JonasSouza871/PolySense-Station-/images/data_analysis/01_Comparison_of_Humidity_Sensor_Distributions_September_Vitória_da_Conquista.png

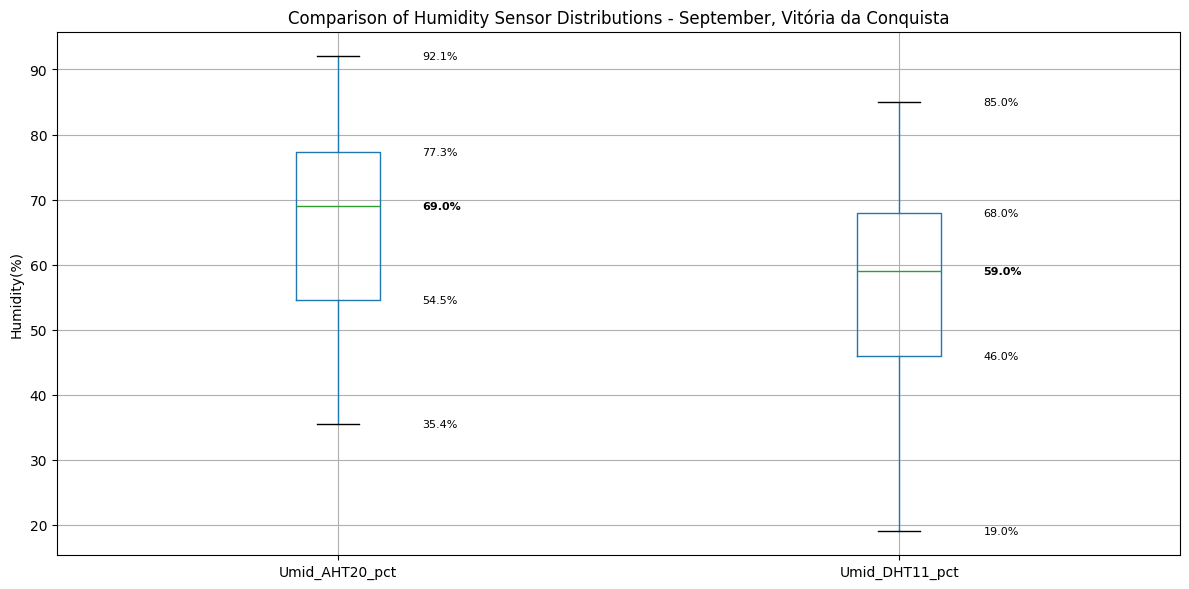
images/data_analysis/01_Comparison_of_Humidity_Sensor_Distributions_September_Vitória_da_Conquista.png
