JonasSouza871/PolySense-Station-/images/data_analysis/01_Humidity_Data_Histogram_in_September_Vitória_da_Conquista.png

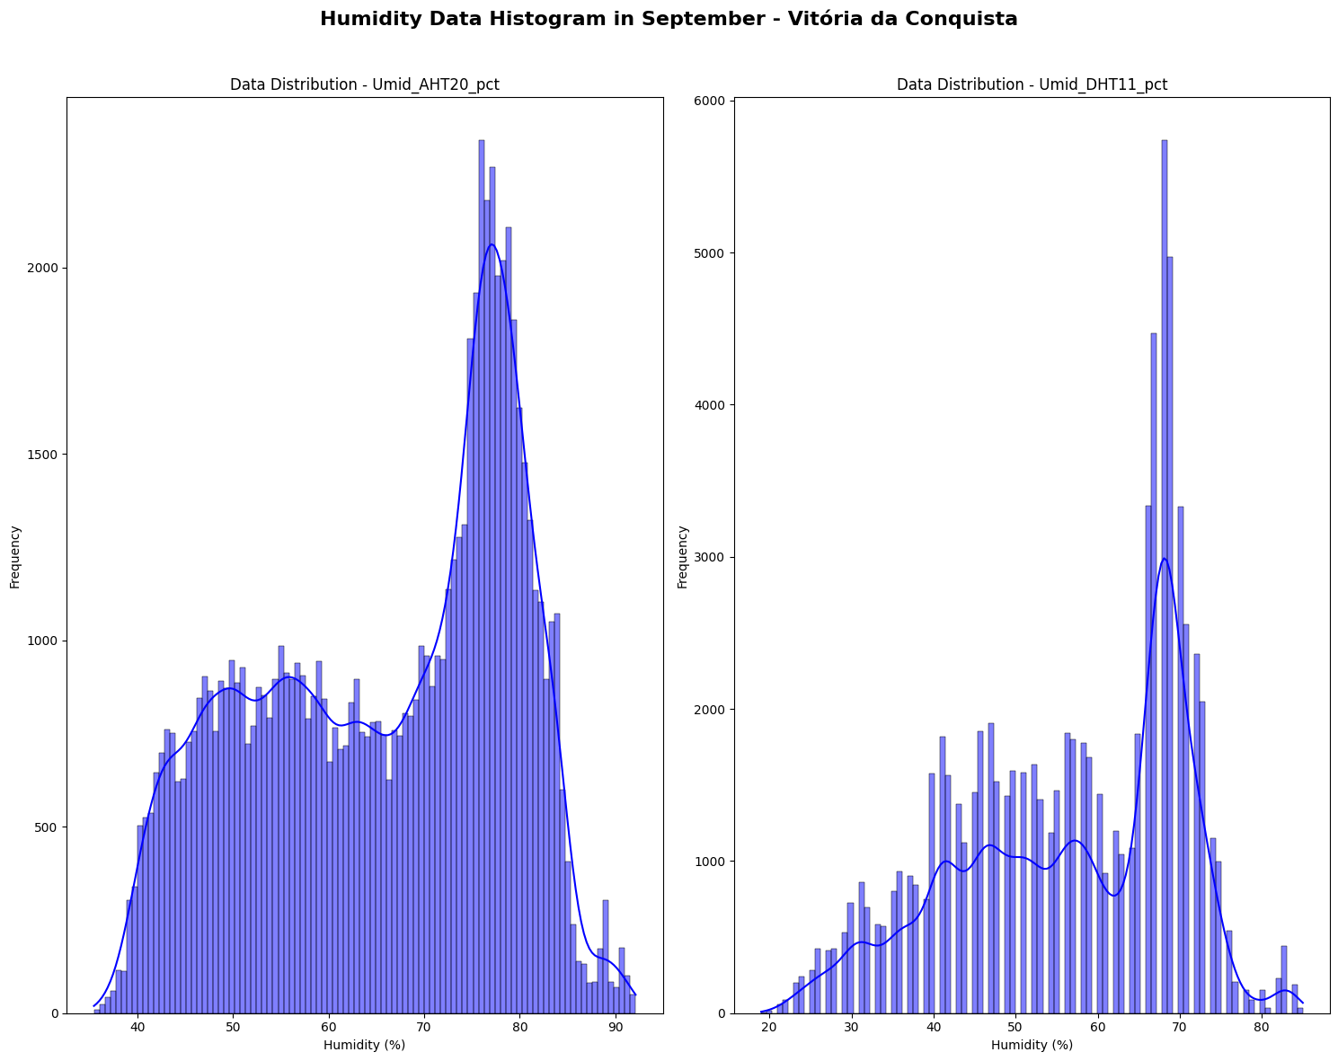
images/data_analysis/01_Humidity_Data_Histogram_in_September_Vitória_da_Conquista.png
