JonasSouza871/PolySense-Station-/images/data_analysis/02_Correlation_Matrix_All_Environmental_SensorsnVitória_da_Conquista_September_2025.png

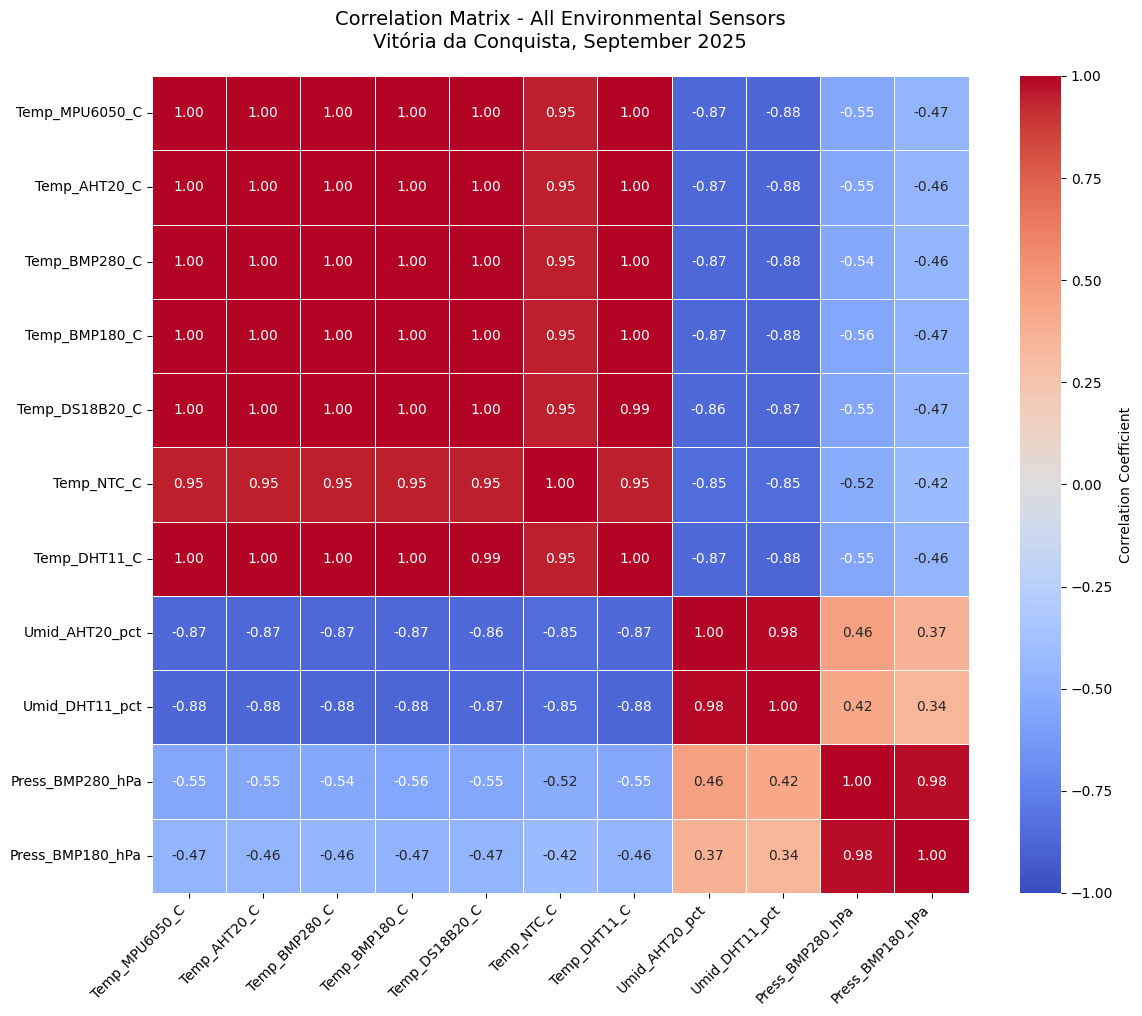
images/data_analysis/02_Correlation_Matrix_All_Environmental_SensorsnVitória_da_Conquista_September_2025.png
