JonasSouza871/PolySense-Station-/images/data_analysis/02_Relationship_between_Humidity_AHT20_and_Pressure_BMP180nVitória_da_Conquista_September_2025.png

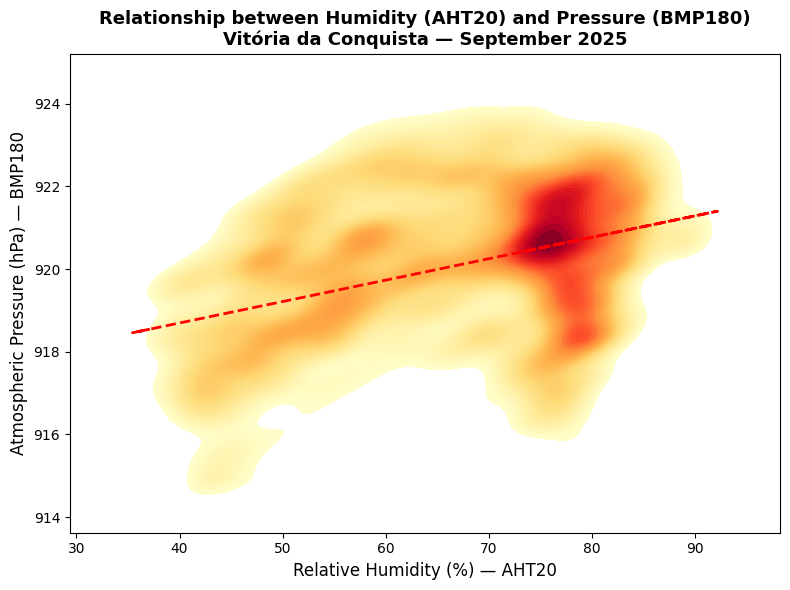
images/data_analysis/02_Relationship_between_Humidity_AHT20_and_Pressure_BMP180nVitória_da_Conquista_September_2025.png
