JonasSouza871/PolySense-Station-/images/data_analysis/02_Relationship_between_Temperature_BMP280_and_Humidity_AHT20nVitória_da_Conquista_September_2025.png

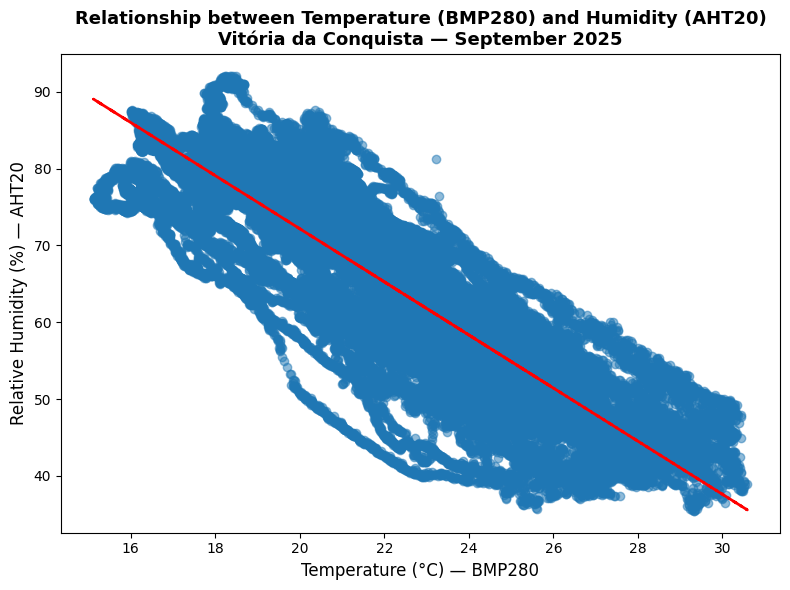
images/data_analysis/02_Relationship_between_Temperature_BMP280_and_Humidity_AHT20nVitória_da_Conquista_September_2025.png
