JonasSouza871/PolySense-Station-/images/data_analysis/03_Data_Completeness_per_Humidity_Sensor_Vitória_da_Conquista_September_2025.png

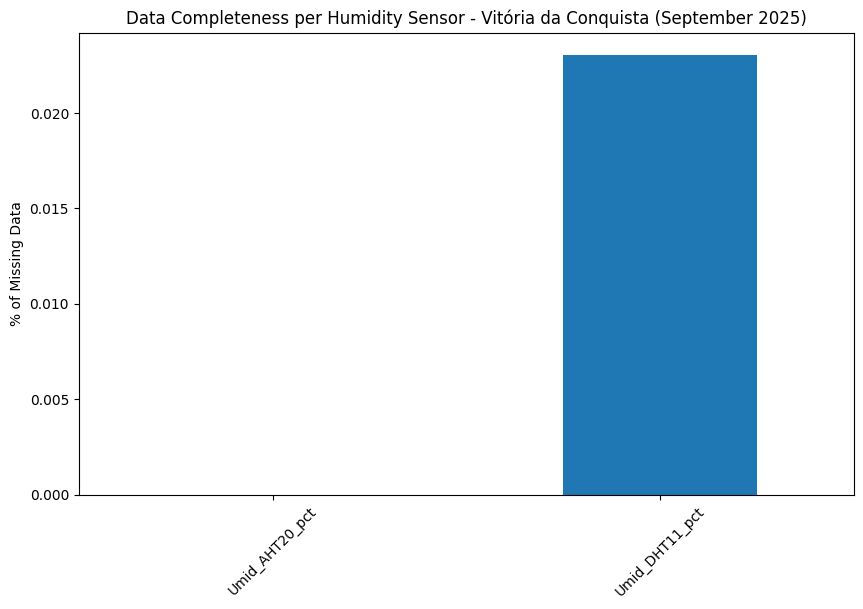
images/data_analysis/03_Data_Completeness_per_Humidity_Sensor_Vitória_da_Conquista_September_2025.png
