JonasSouza871/PolySense-Station-/images/data_analysis/04_BLAND_ALTMAN_ANALYSIS_Humidity_Sensors_vs_Reference_Umi_Ins.png

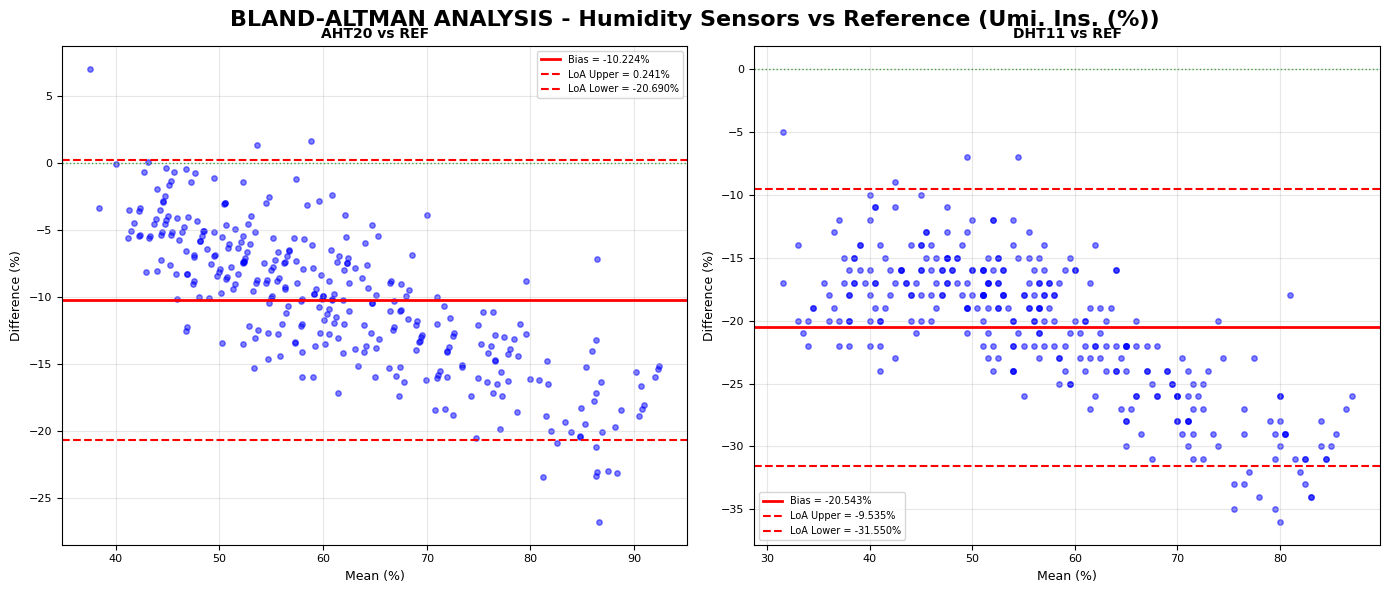
images/data_analysis/04_BLAND_ALTMAN_ANALYSIS_Humidity_Sensors_vs_Reference_Umi_Ins.png
