JonasSouza871/PolySense-Station-/images/data_analysis/04_BLAND_ALTMAN_ANALYSIS_Pressure_Sensors_BMP280_vs_BMP180.png

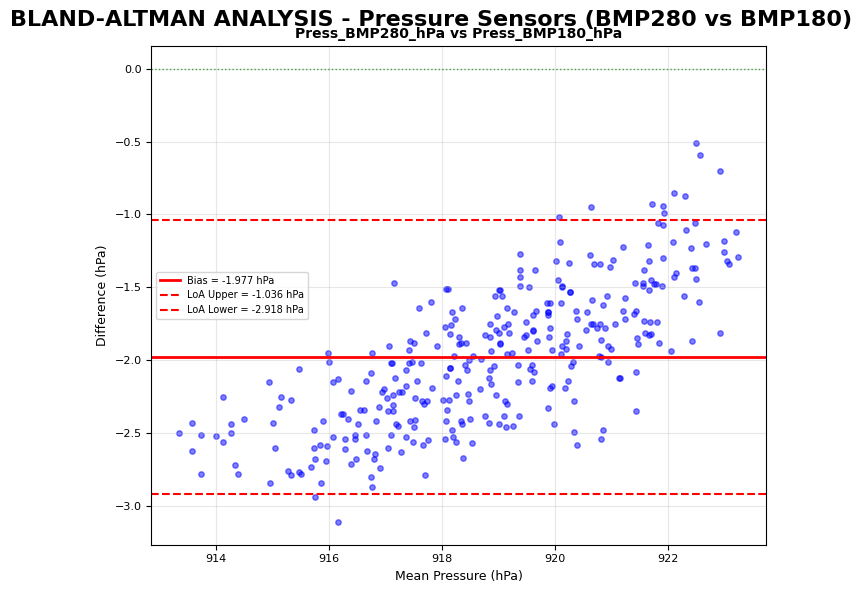
images/data_analysis/04_BLAND_ALTMAN_ANALYSIS_Pressure_Sensors_BMP280_vs_BMP180.png
