JonasSouza871/PolySense-Station-/images/data_analysis/04_BLAND_ALTMAN_ANALYSIS_Pressure_Sensors_vs_Reference_Pressao_Ins_hPa.png

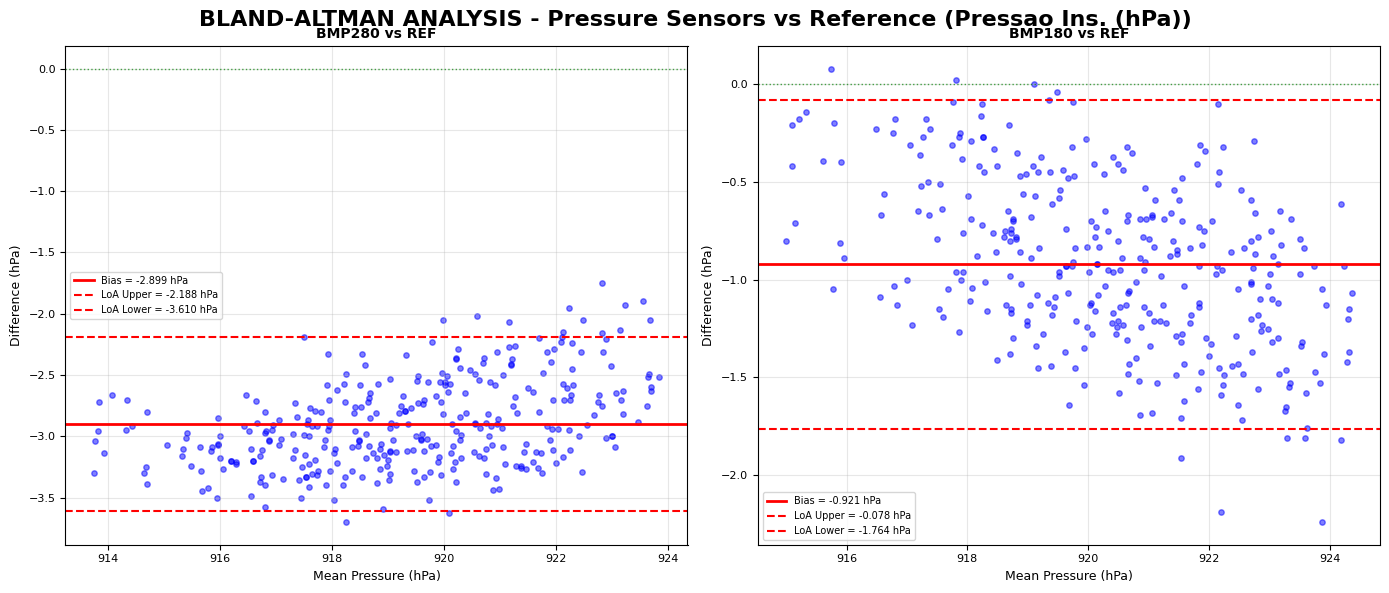
images/data_analysis/04_BLAND_ALTMAN_ANALYSIS_Pressure_Sensors_vs_Reference_Pressao_Ins_hPa.png
