JonasSouza871/PolySense-Station-/images/data_analysis/04_BLAND_ALTMAN_ANALYSIS_Sensors_vs_Reference_Temp_Ins_C.png

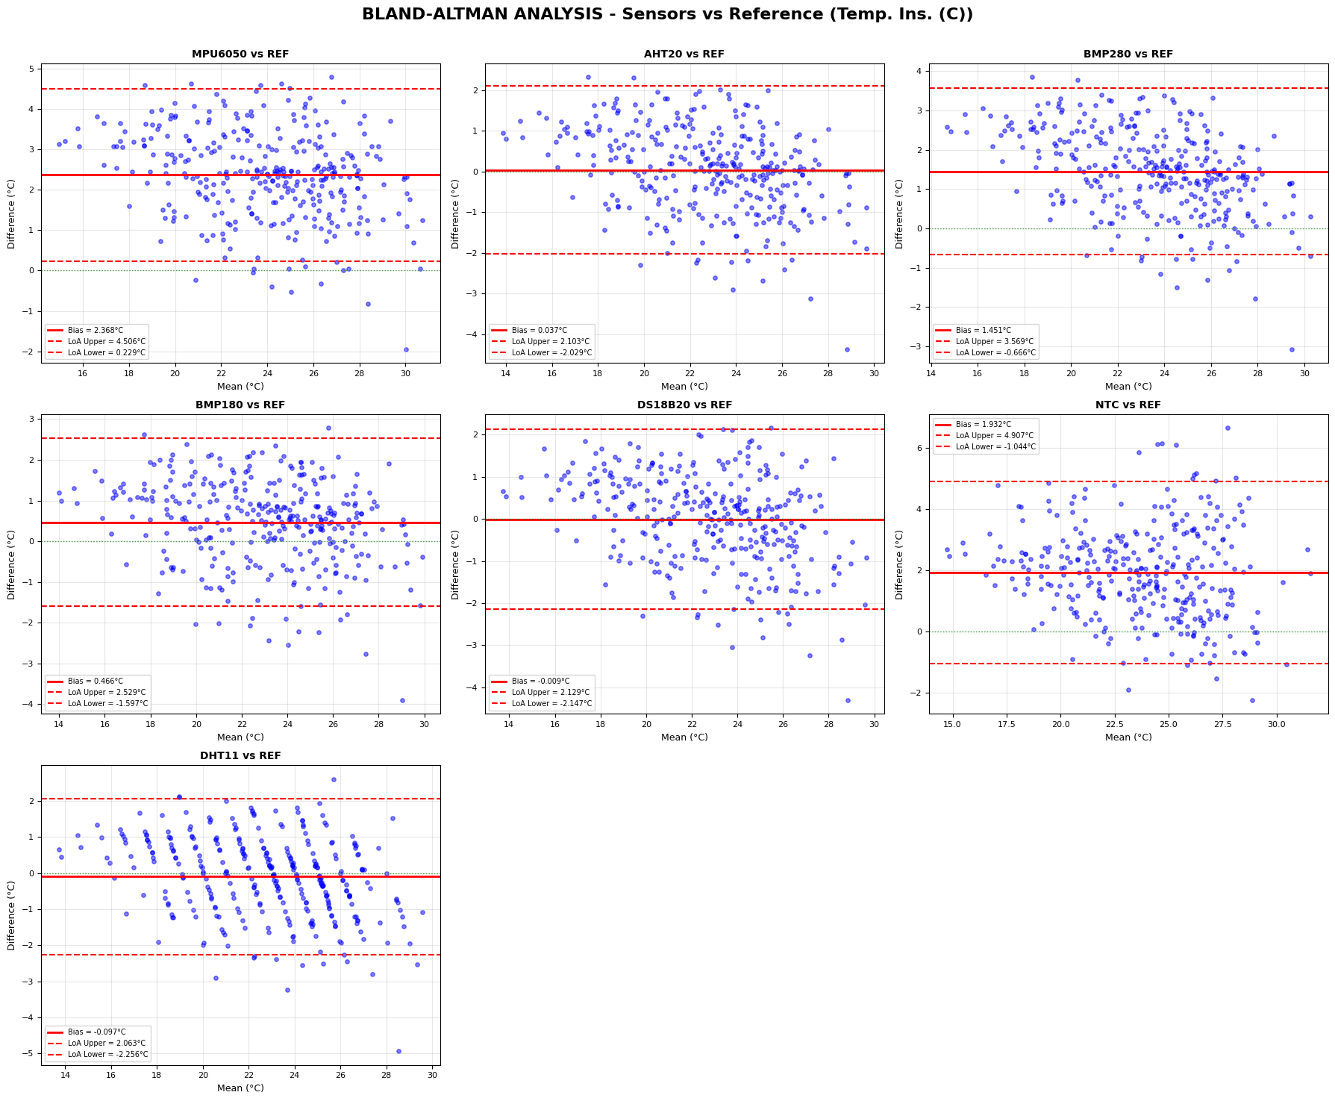
images/data_analysis/04_BLAND_ALTMAN_ANALYSIS_Sensors_vs_Reference_Temp_Ins_C.png
