JonasSouza871/PolySense-Station-/images/data_analysis/04_BLAND_ALTMAN_ANALYSIS_Temperature_Sensors_Pairwise_Comparison.png

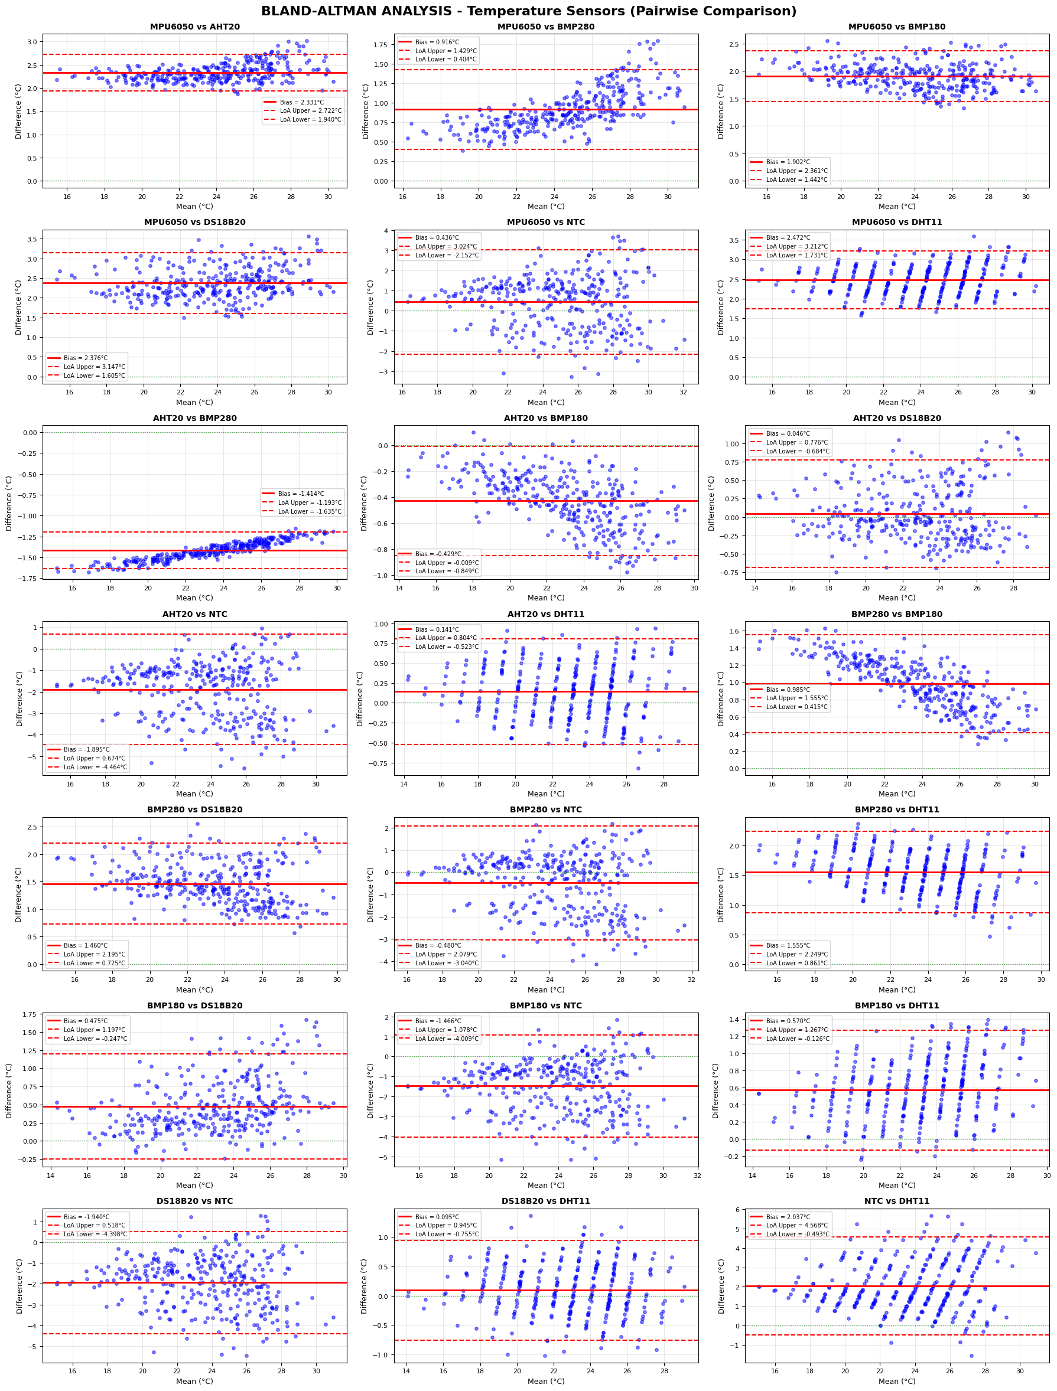
images/data_analysis/04_BLAND_ALTMAN_ANALYSIS_Temperature_Sensors_Pairwise_Comparison.png
