JonasSouza871/PolySense-Station-/images/data_analysis/05_Humidity_Sensors_Comparison_September_2025_Vitória_da_Conquista.png

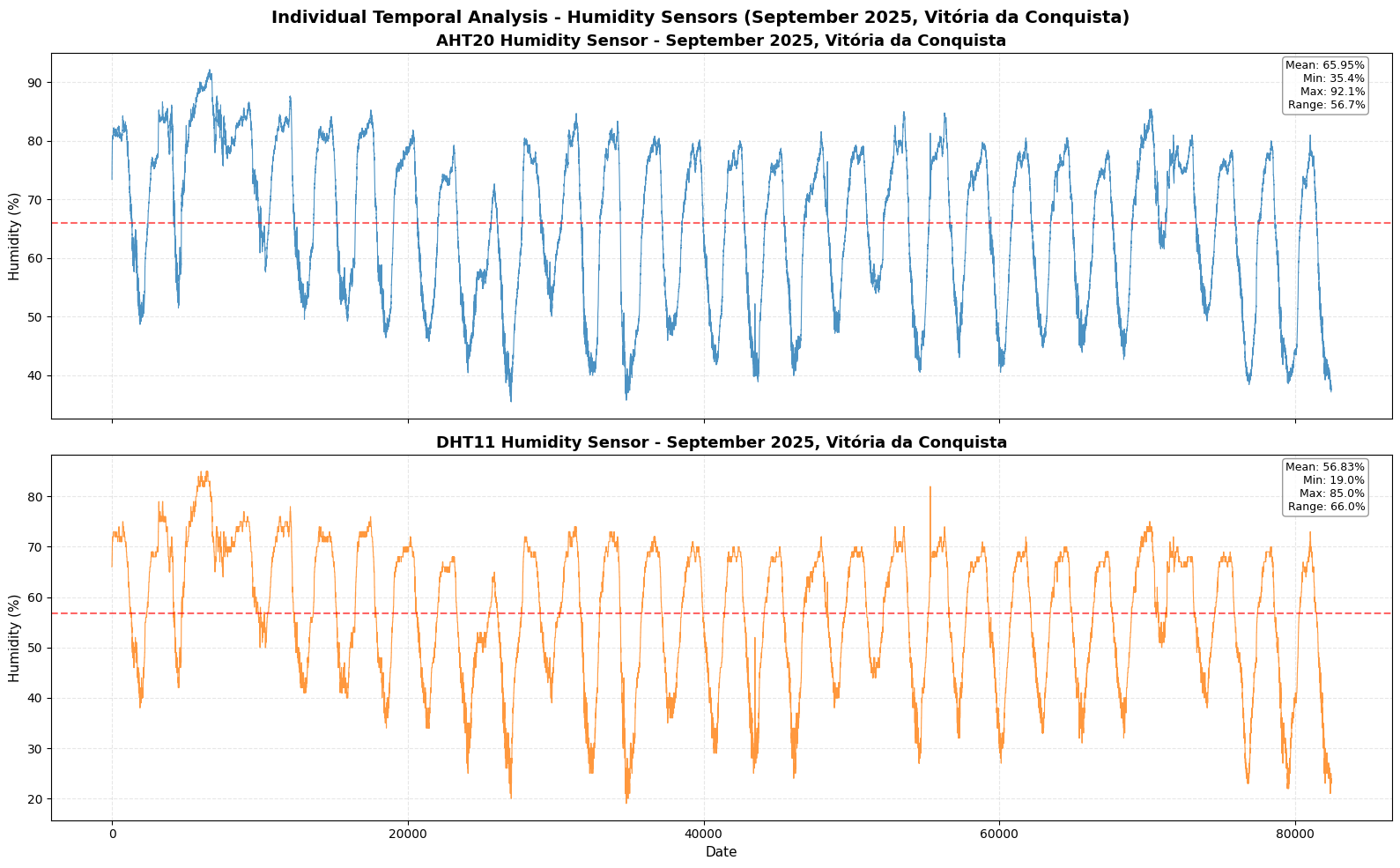
images/data_analysis/05_Humidity_Sensors_Comparison_September_2025_Vitória_da_Conquista.png
