JonasSouza871/PolySense-Station-/images/data_analysis/05_Pressure_Sensors_Comparison_September_2025_Vitória_da_Conquista_1.png

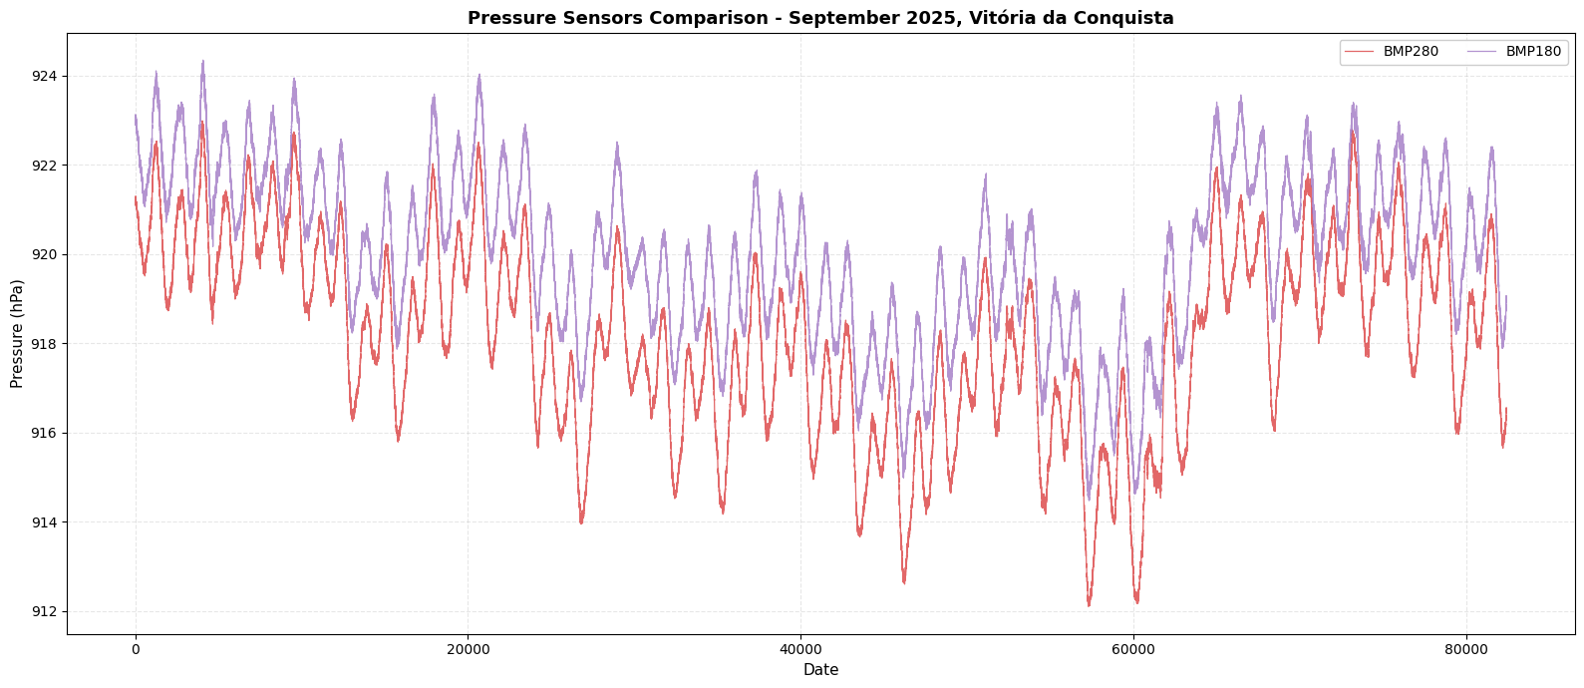
images/data_analysis/05_Pressure_Sensors_Comparison_September_2025_Vitória_da_Conquista_1.png
