JonasSouza871/PolySense-Station-/images/data_analysis/05_Temporal_Analysis_plot_07.png

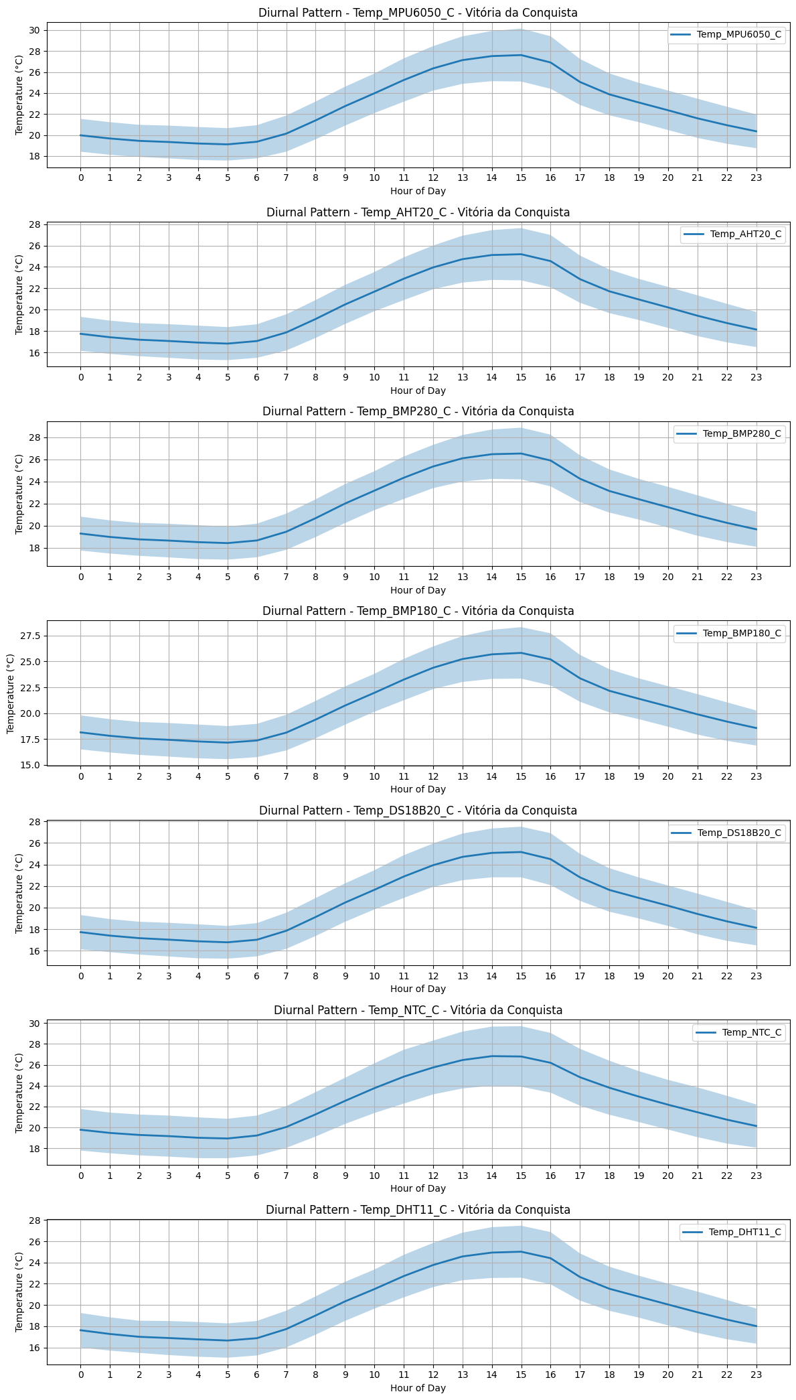
images/data_analysis/05_Temporal_Analysis_plot_07.png
