JonasSouza871/PolySense-Station-/images/data_analysis/06_Time_Series_Decomposition_plot_07.png

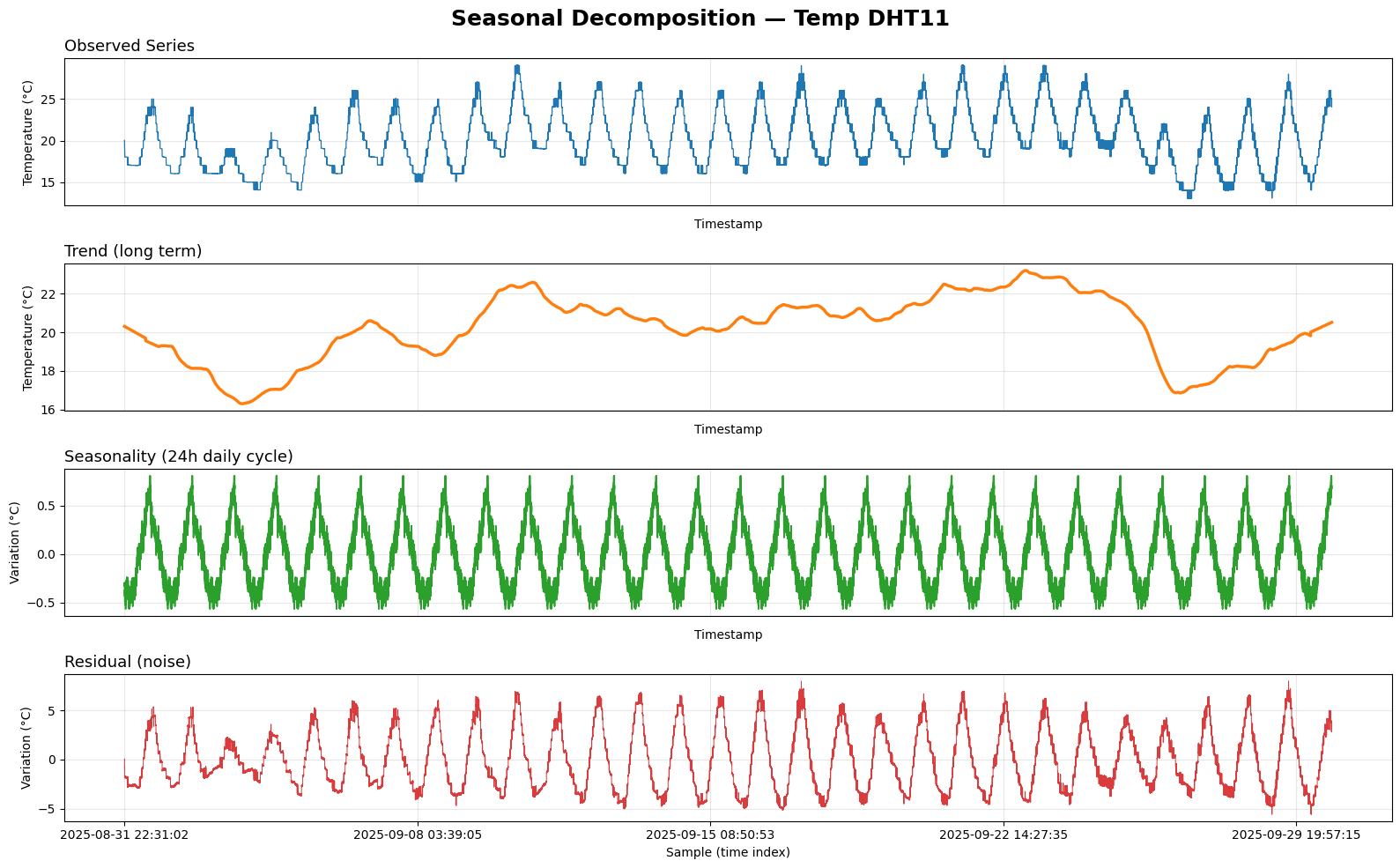
images/data_analysis/06_Time_Series_Decomposition_plot_07.png
