JonasSouza871/PolySense-Station-/images/data_analysis/06_Time_Series_Decomposition_plot_08.png

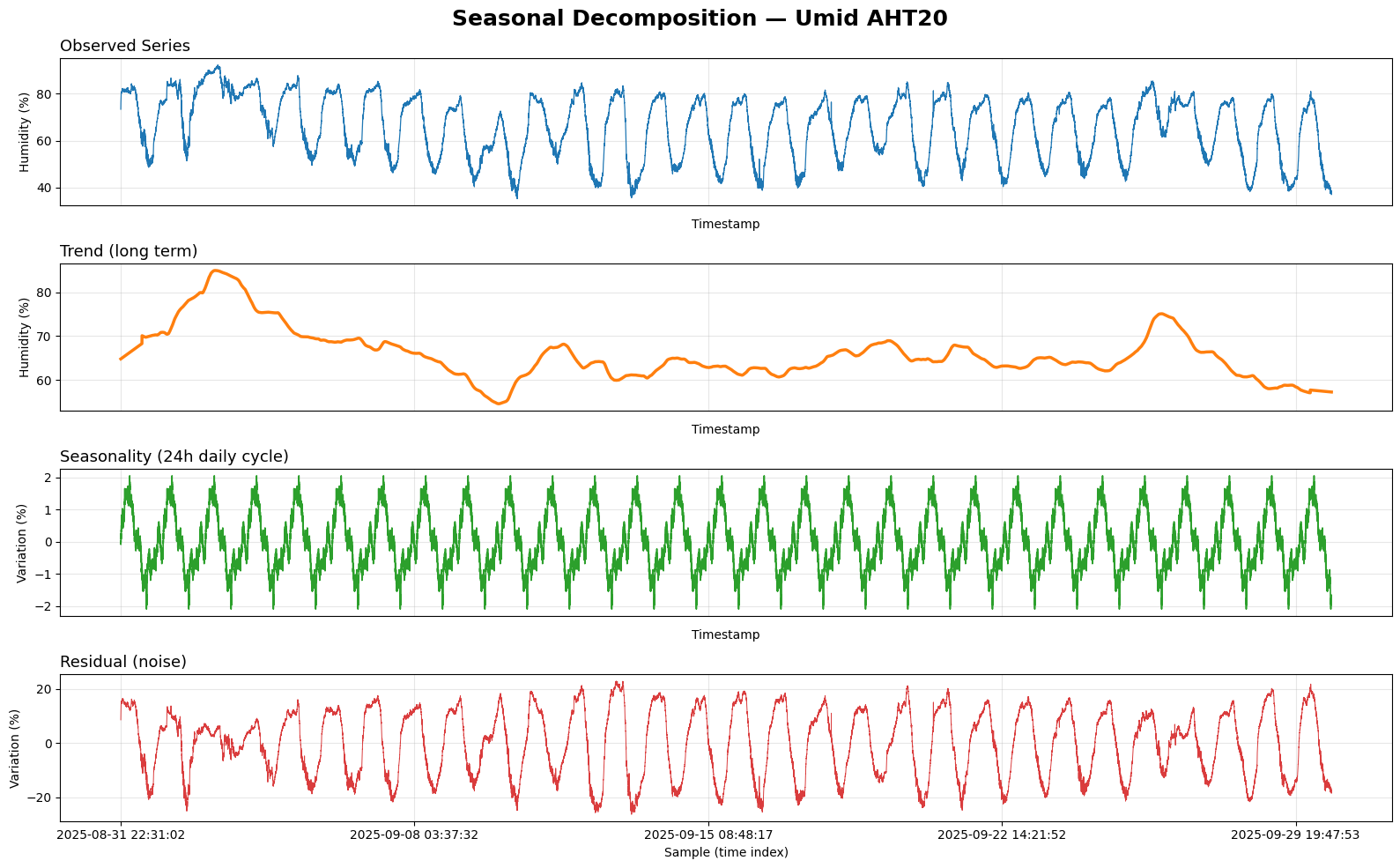
images/data_analysis/06_Time_Series_Decomposition_plot_08.png
