JonasSouza871/PolySense-Station-/images/data_analysis/06_Time_Series_Decomposition_plot_09.png

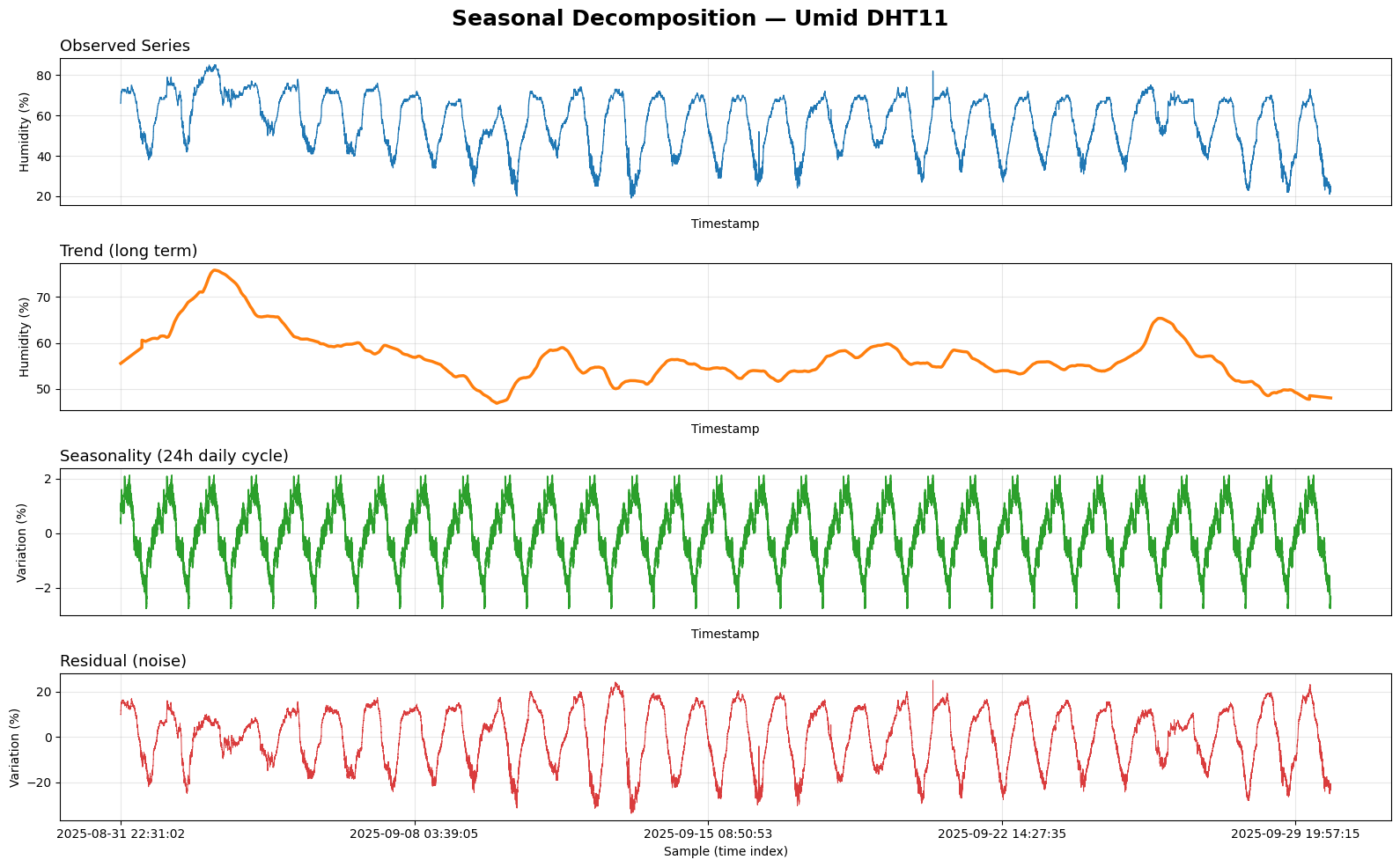
images/data_analysis/06_Time_Series_Decomposition_plot_09.png
