JonasSouza871/PolySense-Station-/images/machine_learning/07_Anomaly_Detection_plot_03.png

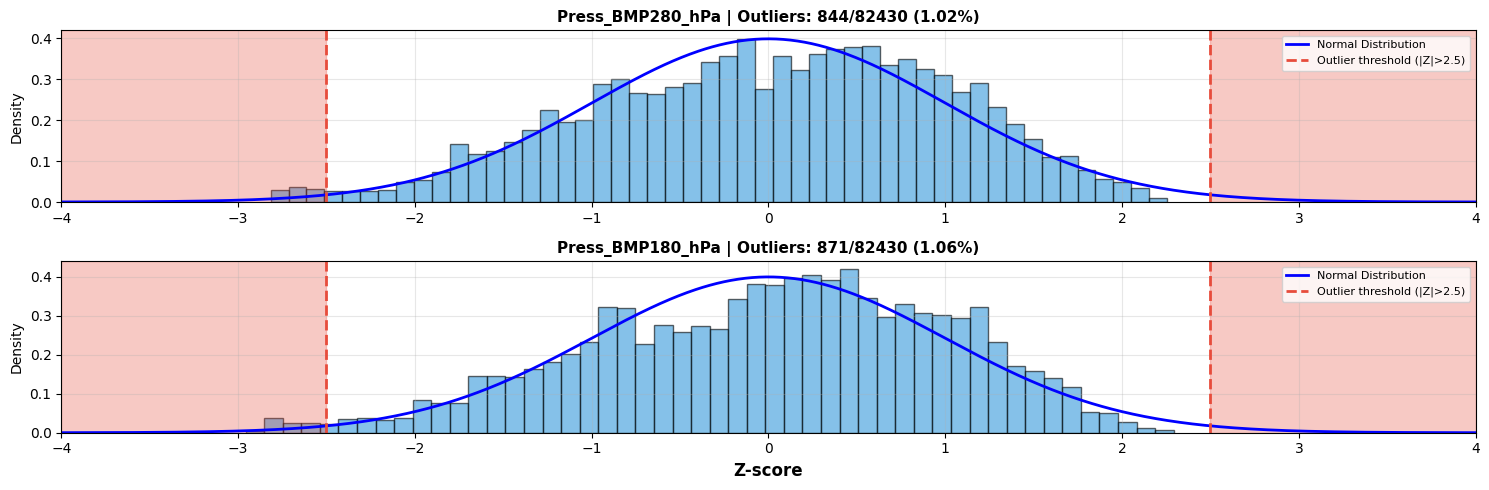
images/machine_learning/07_Anomaly_Detection_plot_03.png
