JonasSouza871/PolySense-Station-/images/machine_learning/07_Heatmap_Sensor_Deviations_in_Detected_AnomaliesnRed_High_deviation_Green_Normal_showing_50_random_anomalies_2.png

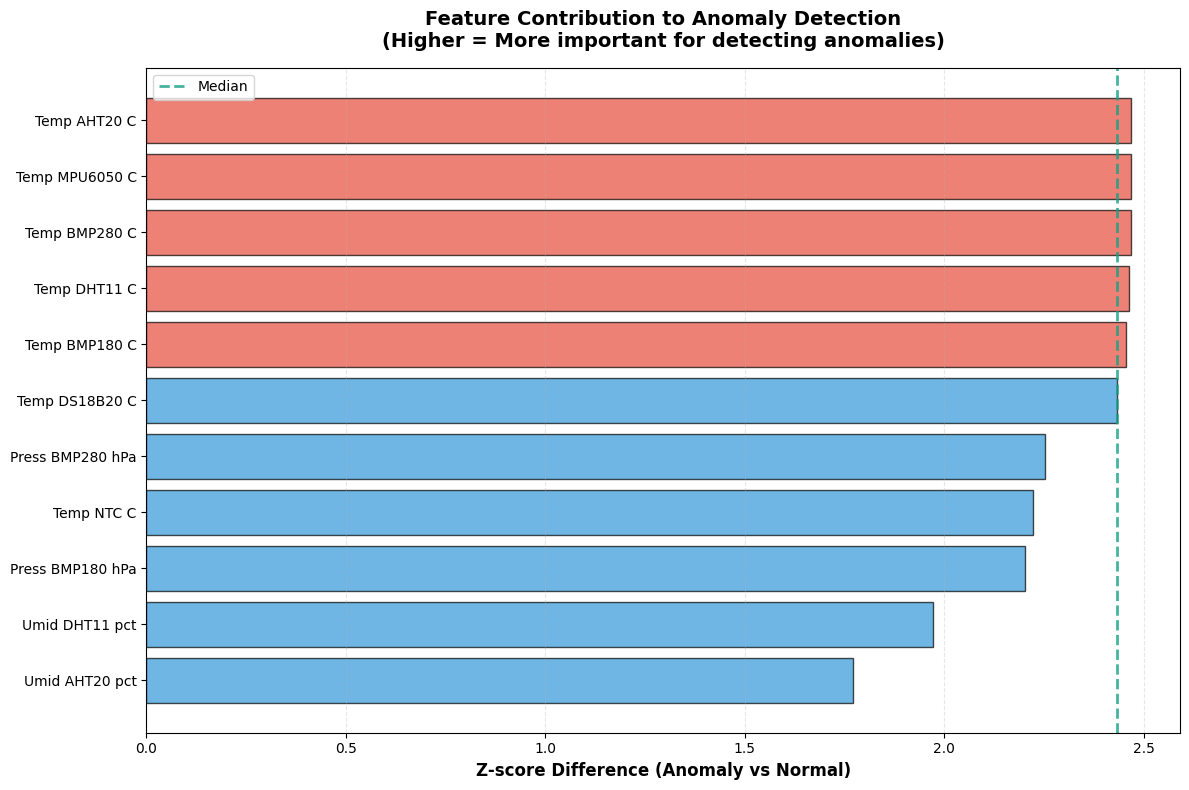
images/machine_learning/07_Heatmap_Sensor_Deviations_in_Detected_AnomaliesnRed_High_deviation_Green_Normal_showing_50_random_anomalies_2.png
