JonasSouza871/PolySense-Station-/images/machine_learning/07_Isolation_Forest_Anomaly_Detection_Across_All_Sensors.png

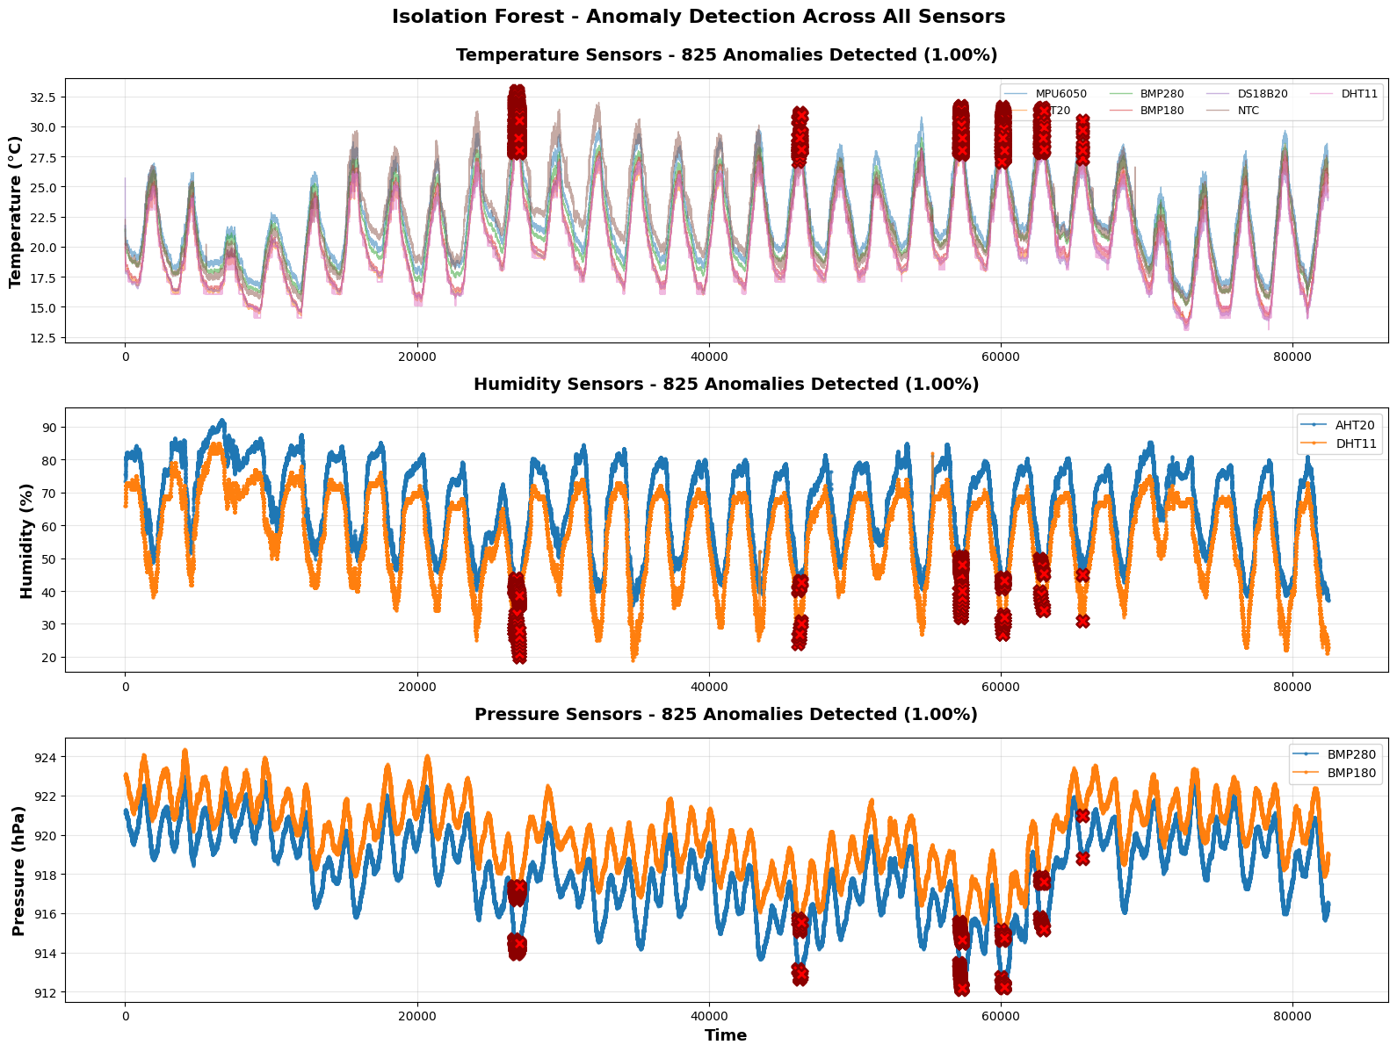
images/machine_learning/07_Isolation_Forest_Anomaly_Detection_Across_All_Sensors.png
