JonasSouza871/PolySense-Station-/images/machine_learning/07_Stuck_Values_Detection_Δ_001C.png

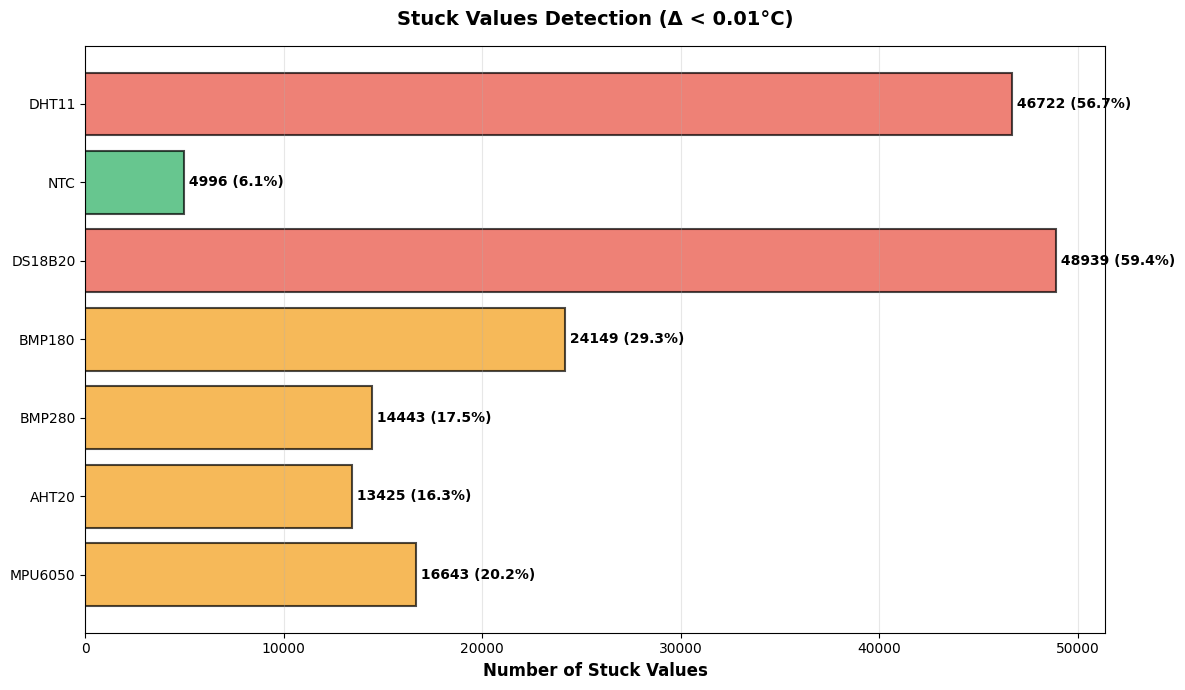
images/machine_learning/07_Stuck_Values_Detection_Δ_001C.png
