JonasSouza871/PolySense-Station-/images/machine_learning/08_Which_Variable_Most_Influences_the_Analysis_Vitória_da_Conquista_September_2025.png

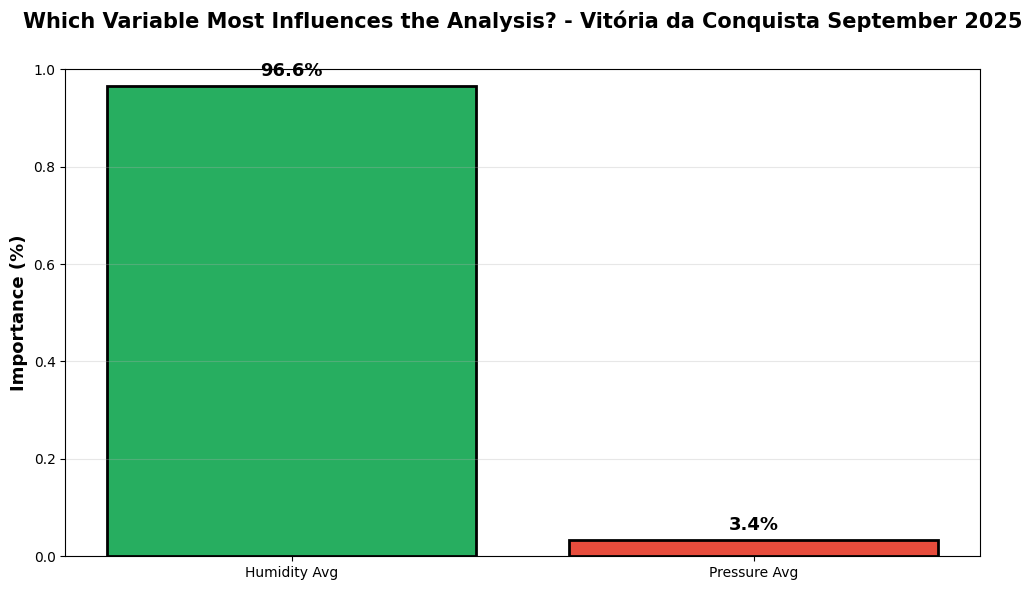
images/machine_learning/08_Which_Variable_Most_Influences_the_Analysis_Vitória_da_Conquista_September_2025.png
