JonasSouza871/PolySense-Station-/images/machine_learning/09_3D_Climate_Clustering_GMM_K4nVitória_da_Conquista_September_2025.png

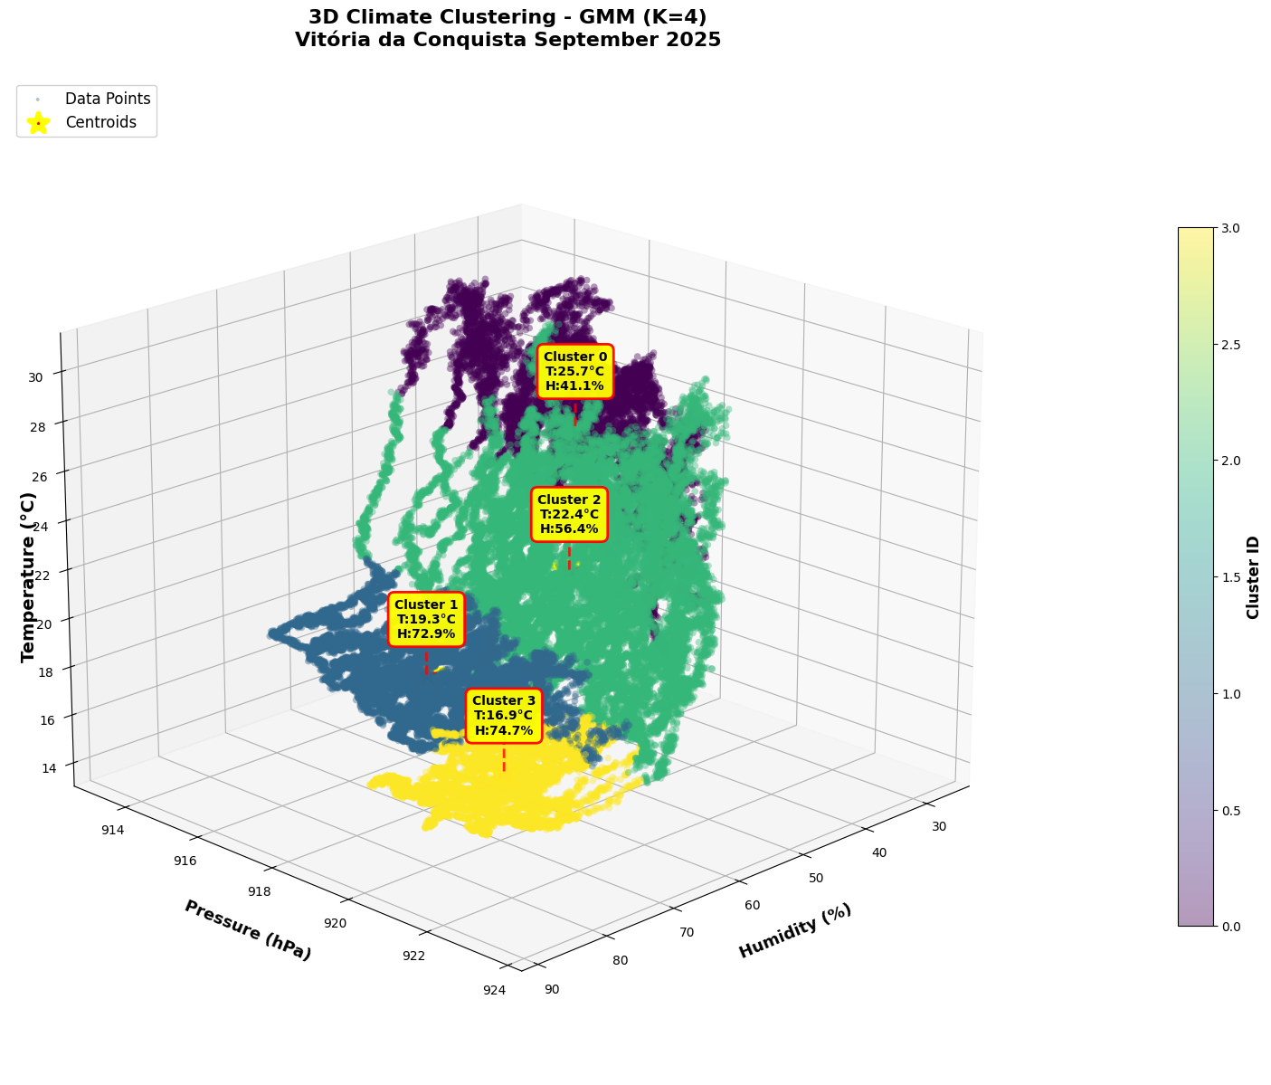
images/machine_learning/09_3D_Climate_Clustering_GMM_K4nVitória_da_Conquista_September_2025.png
