JonasSouza871/PolySense-Station-/images/machine_learning/10_KMeans_Clustering_plot_01.png

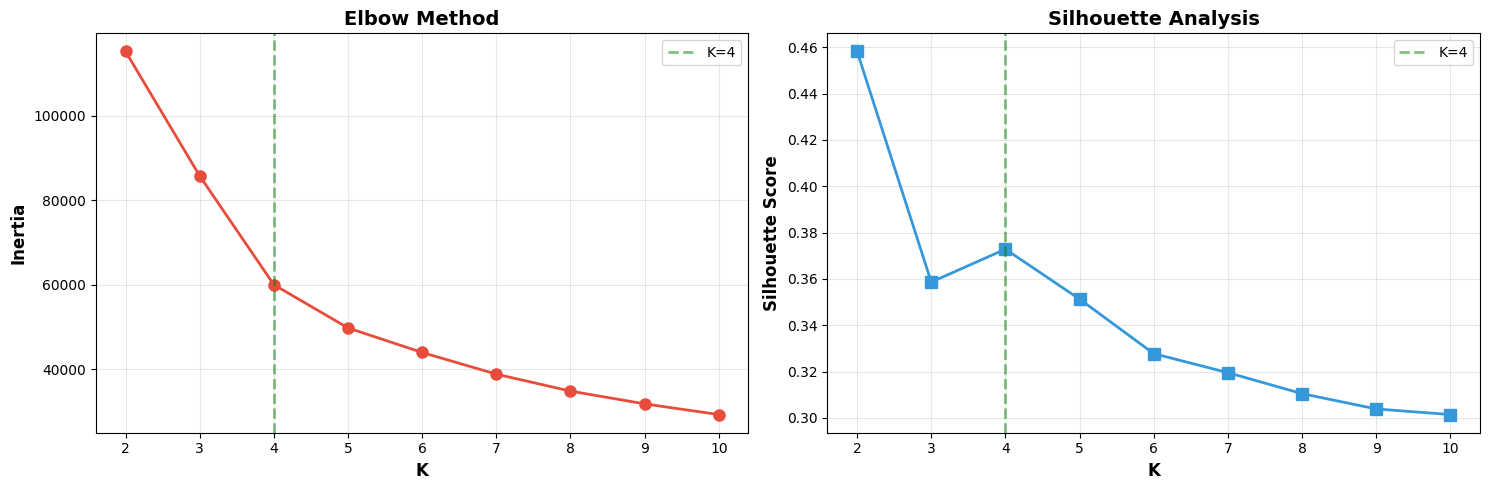
images/machine_learning/10_KMeans_Clustering_plot_01.png
