JonasSouza871/PolySense-Station-/images/machine_learning/11_Error_Evolution_During_Training.png

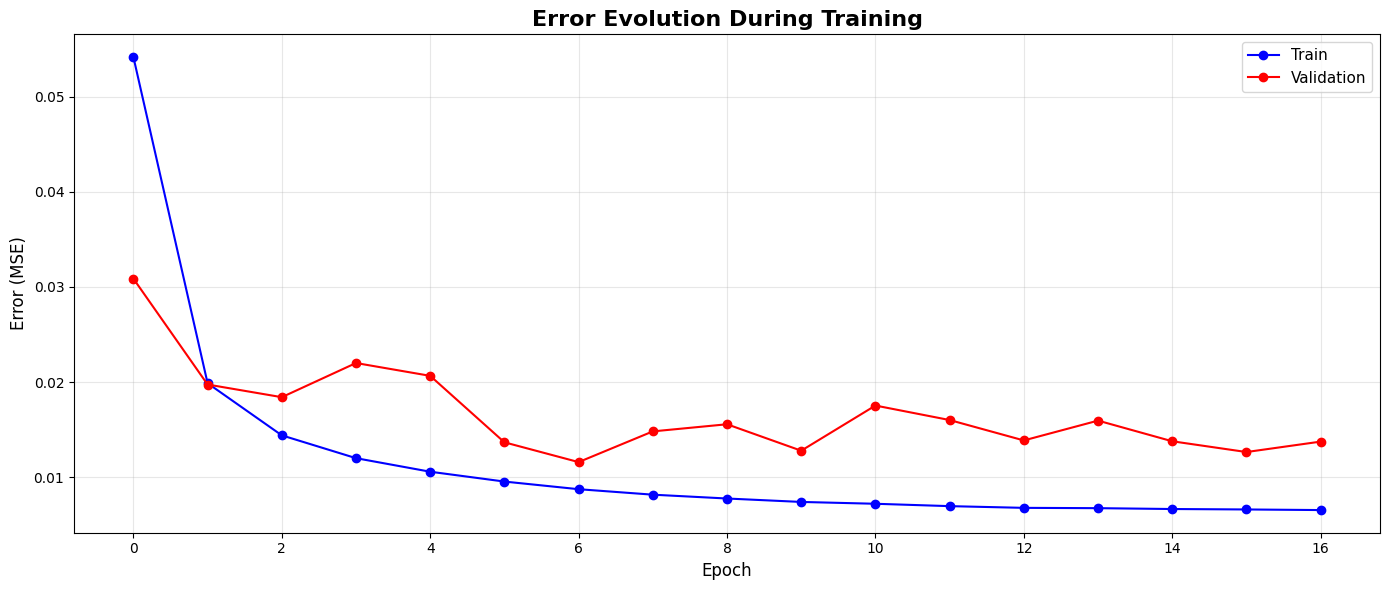
images/machine_learning/11_Error_Evolution_During_Training.png
