JonasSouza871/PolySense-Station-/images/machine_learning/11_Real_Temperature_vs_Model_Prediction_Vitória_da_Conquista_in_the_Last_Week_of_September_2025.png

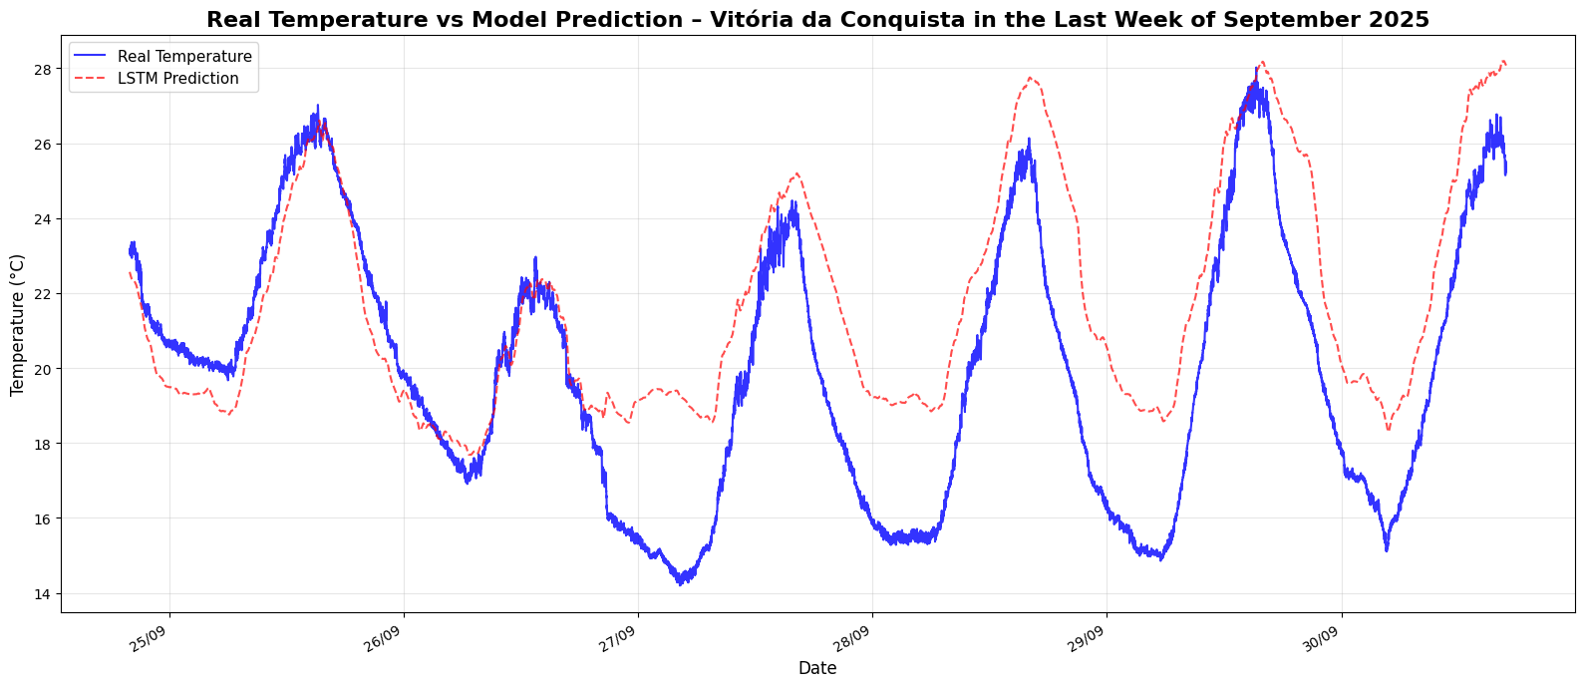
images/machine_learning/11_Real_Temperature_vs_Model_Prediction_Vitória_da_Conquista_in_the_Last_Week_of_September_2025.png
