JonasSouza871/PolySense-Station-/images/signal_processing/12_Humidity_Analysis_Panel_Complete_View_Raw_vs_FilterednVitoria_da_Conquista_September_2025_2.png

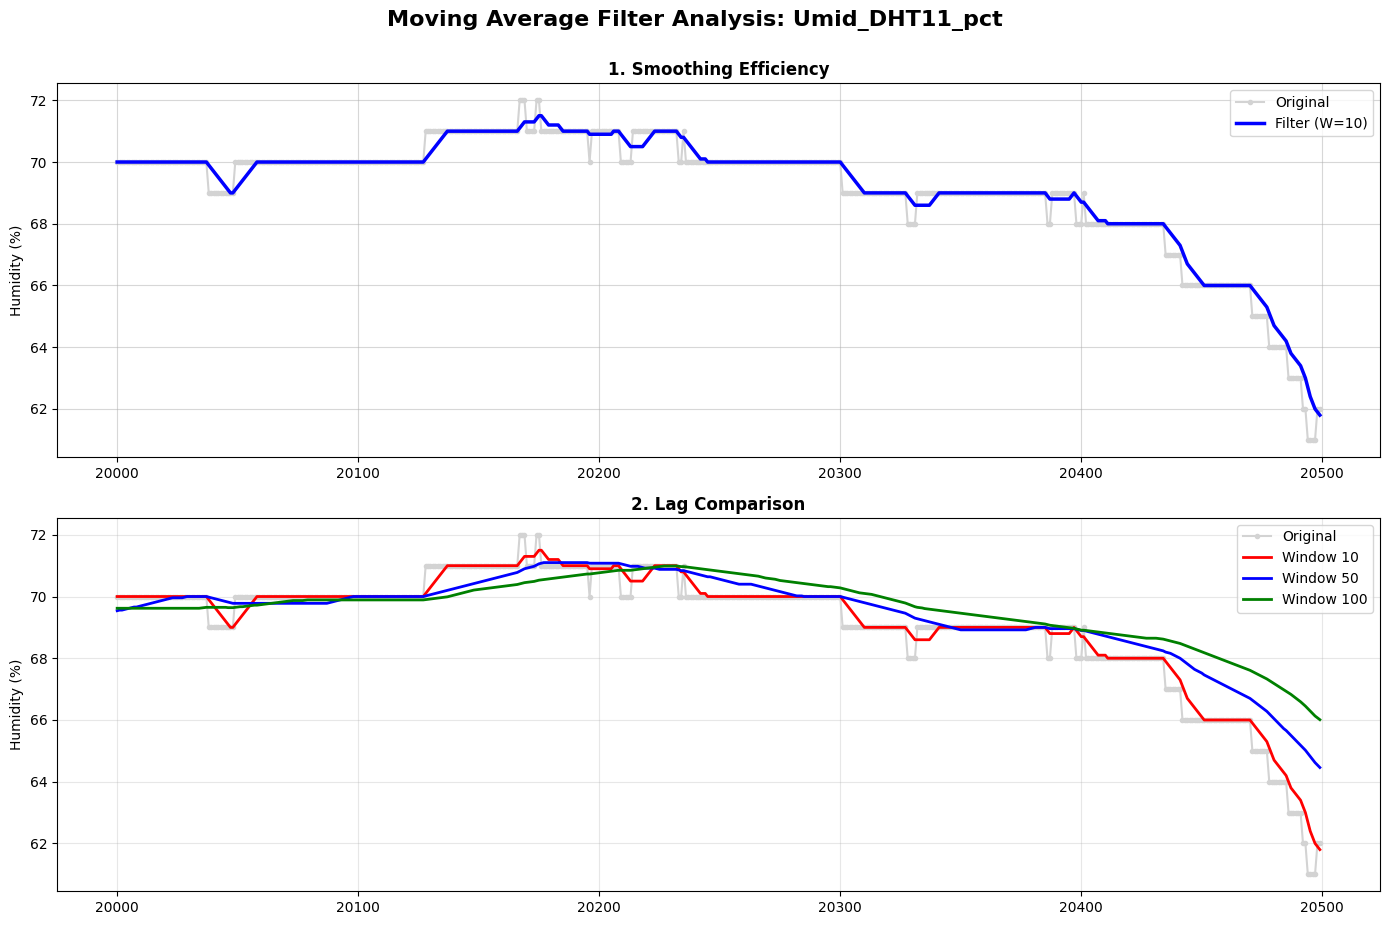
images/signal_processing/12_Humidity_Analysis_Panel_Complete_View_Raw_vs_FilterednVitoria_da_Conquista_September_2025_2.png
