JonasSouza871/PolySense-Station-/images/signal_processing/12_Temperature_Analysis_Panel_Complete_View_Raw_vs_Median_FilterednVitoria_da_Conquista_September_2025_5.png

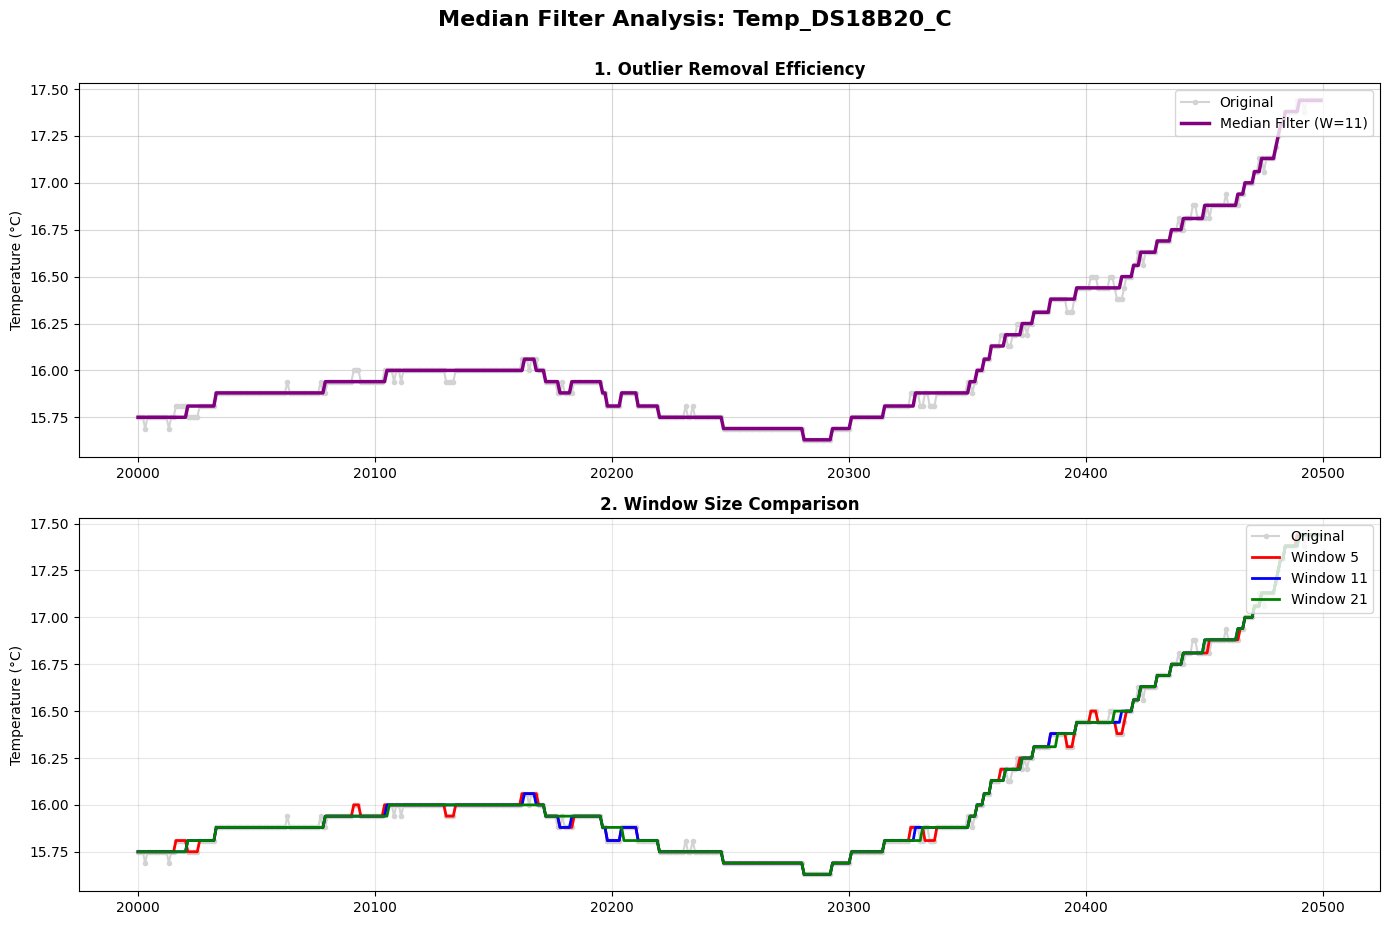
images/signal_processing/12_Temperature_Analysis_Panel_Complete_View_Raw_vs_Median_FilterednVitoria_da_Conquista_September_2025_5.png
