JonasSouza871/PolySense-Station-/images/signal_processing/13_FFT_Frequency_Analysis_plot_02.png

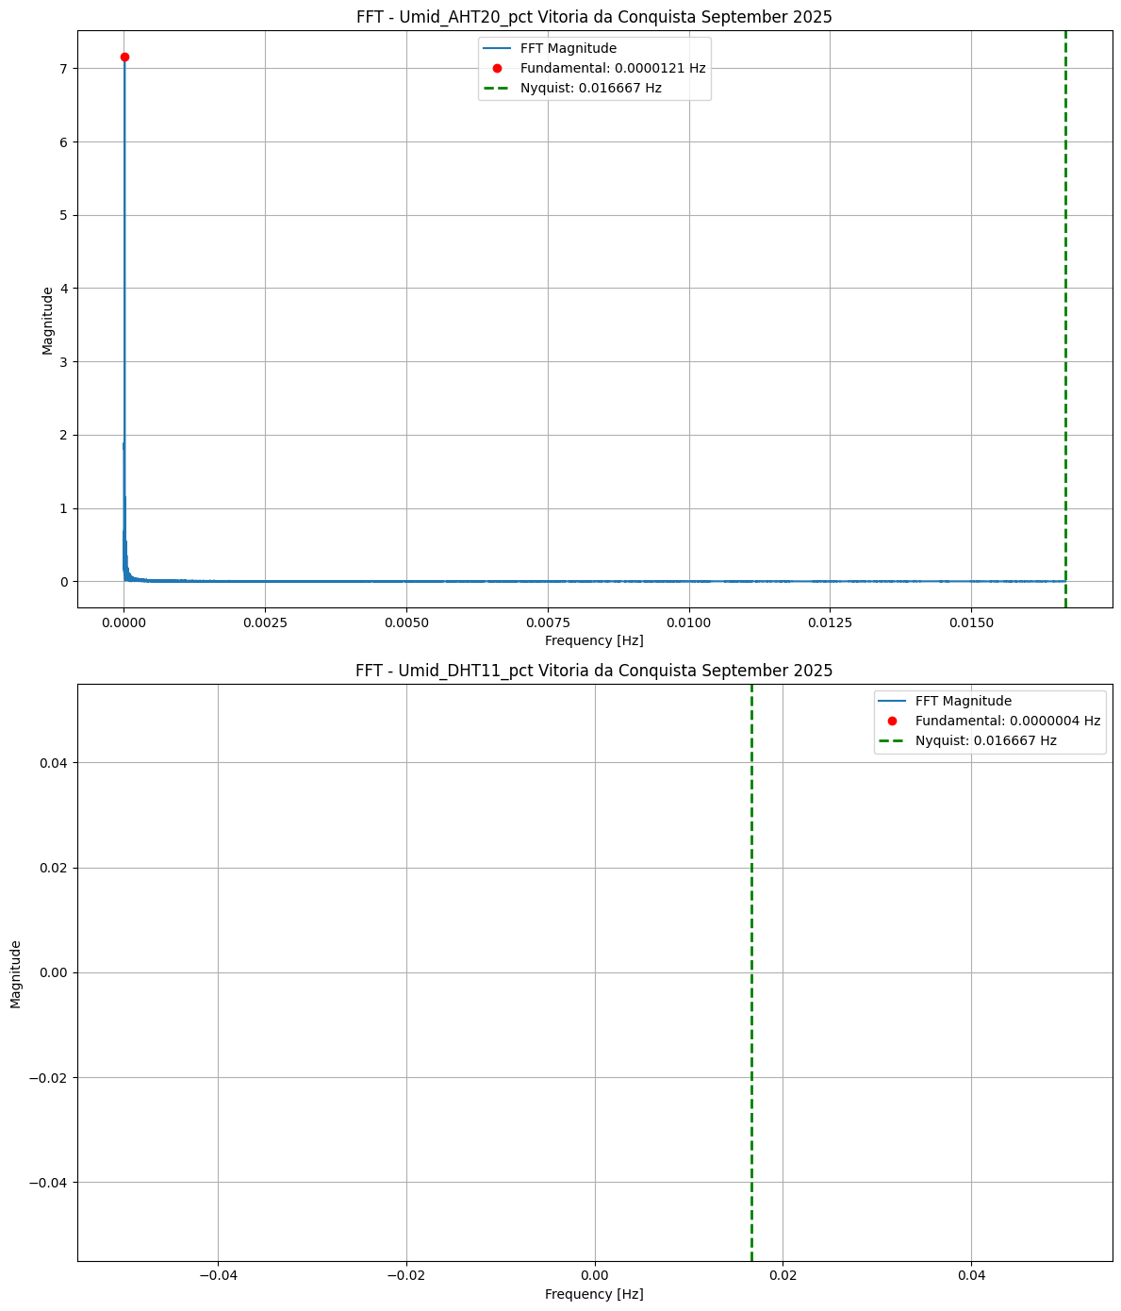
images/signal_processing/13_FFT_Frequency_Analysis_plot_02.png
