JonasSouza871/PolySense-Station-/images/data_analysis/04_Sensor_Comparison_and_Validation_plot_07.png

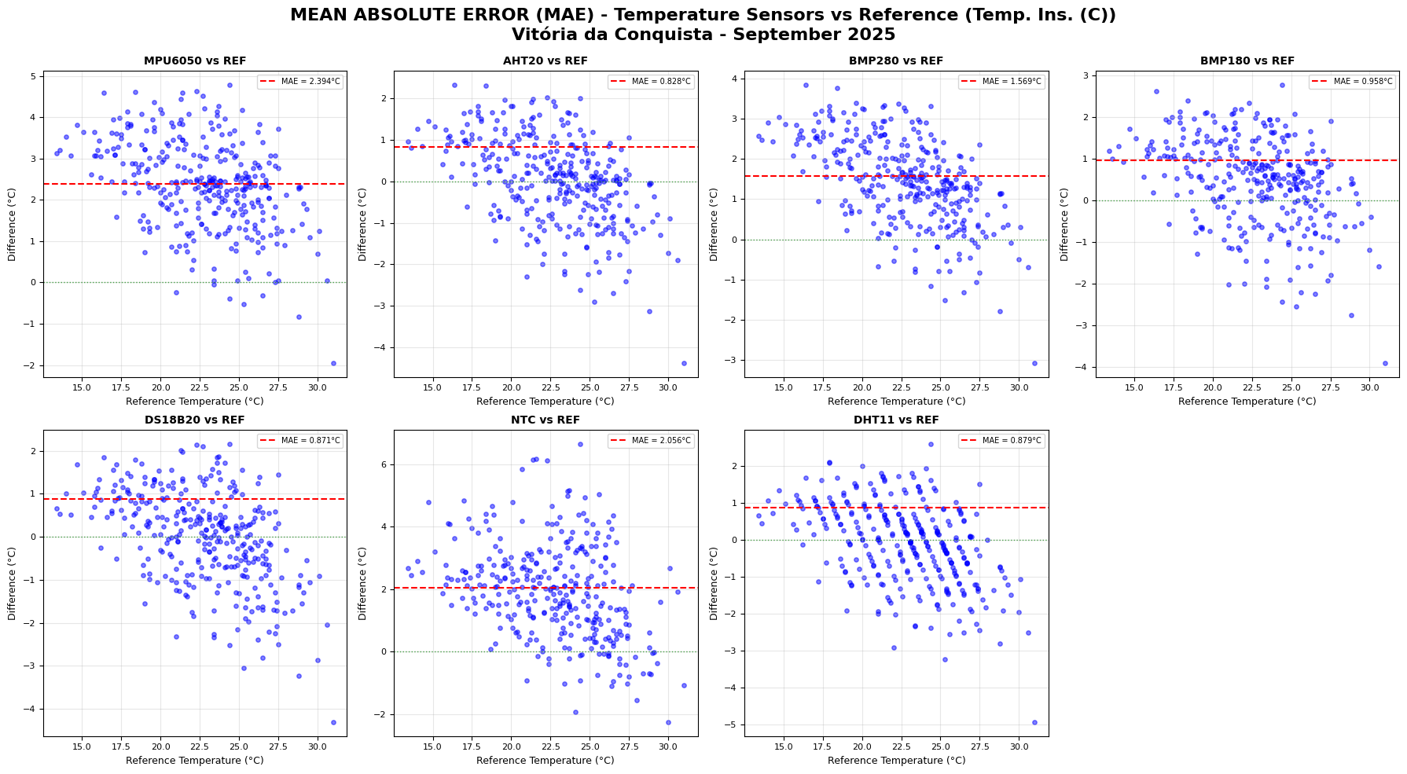
images/data_analysis/04_Sensor_Comparison_and_Validation_plot_07.png
